satria-mitra/CASA0022-Water-Scout/3D Parts/Solar Panel/two_way_bracket.stl

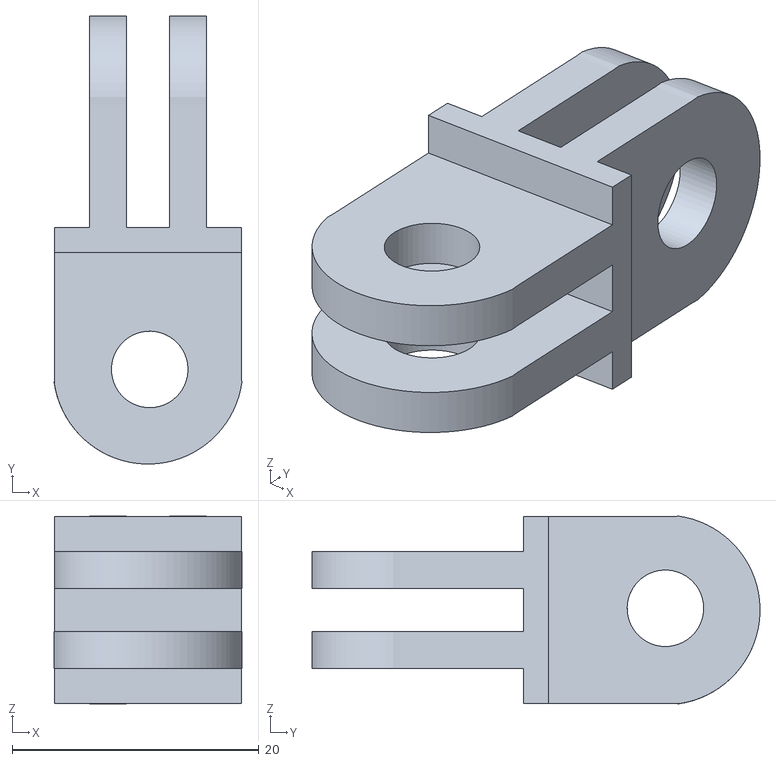
[picture p17: CAD file, 2024-08-15]
3D Parts/Solar Panel/two_way_bracket.stl
15.2 x 36.3 x 15.2
