satria-mitra/CASA0022-Water-Scout/3D Parts/Solar Panel/back_bracket v1.stl

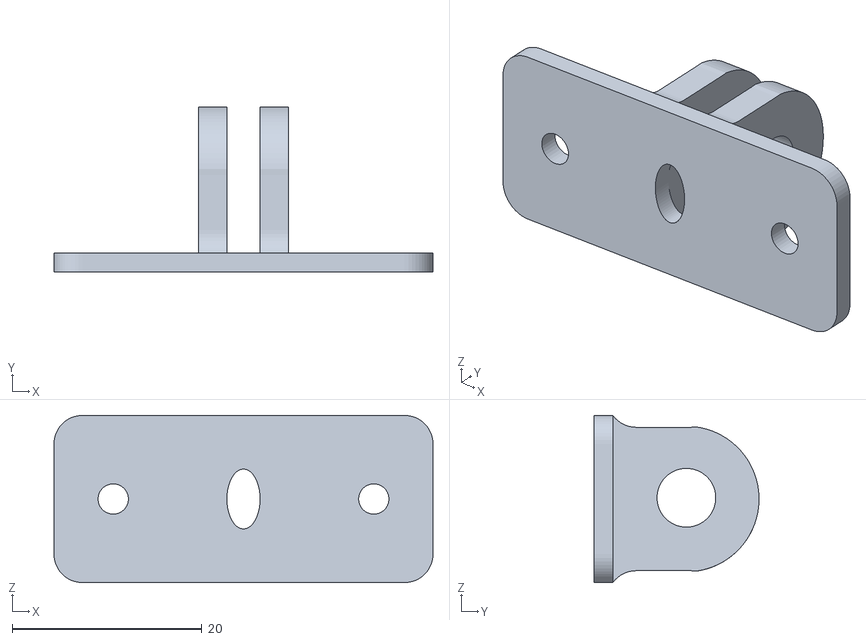
[picture p18: CAD file, 2024-08-15, an earlier design]
3D Parts/Solar Panel/back_bracket v1.stl
40.0 x 17.4 x 17.6
