satria-mitra/CASA0022-Water-Scout/Arduino/DYP-A01/arduino_secrets.h

// Replace with keys obtained from TheThingsNetwork console
#define SECRET_APP_EUI "0000000000000000"
//#define SECRET_APP_KEY "C604BD3E8DE06FBBBA2C9F82C5815702"


#define SECRET_APP_KEY "F503C9AA3F9E6C99673DD4578ADC9A13"
